SolderedElectronics/USB-UART-CH340C-converter-board-hardware-design/OUTPUTS/V1.2.0/USB-UART CH340C converter board Pinout.png

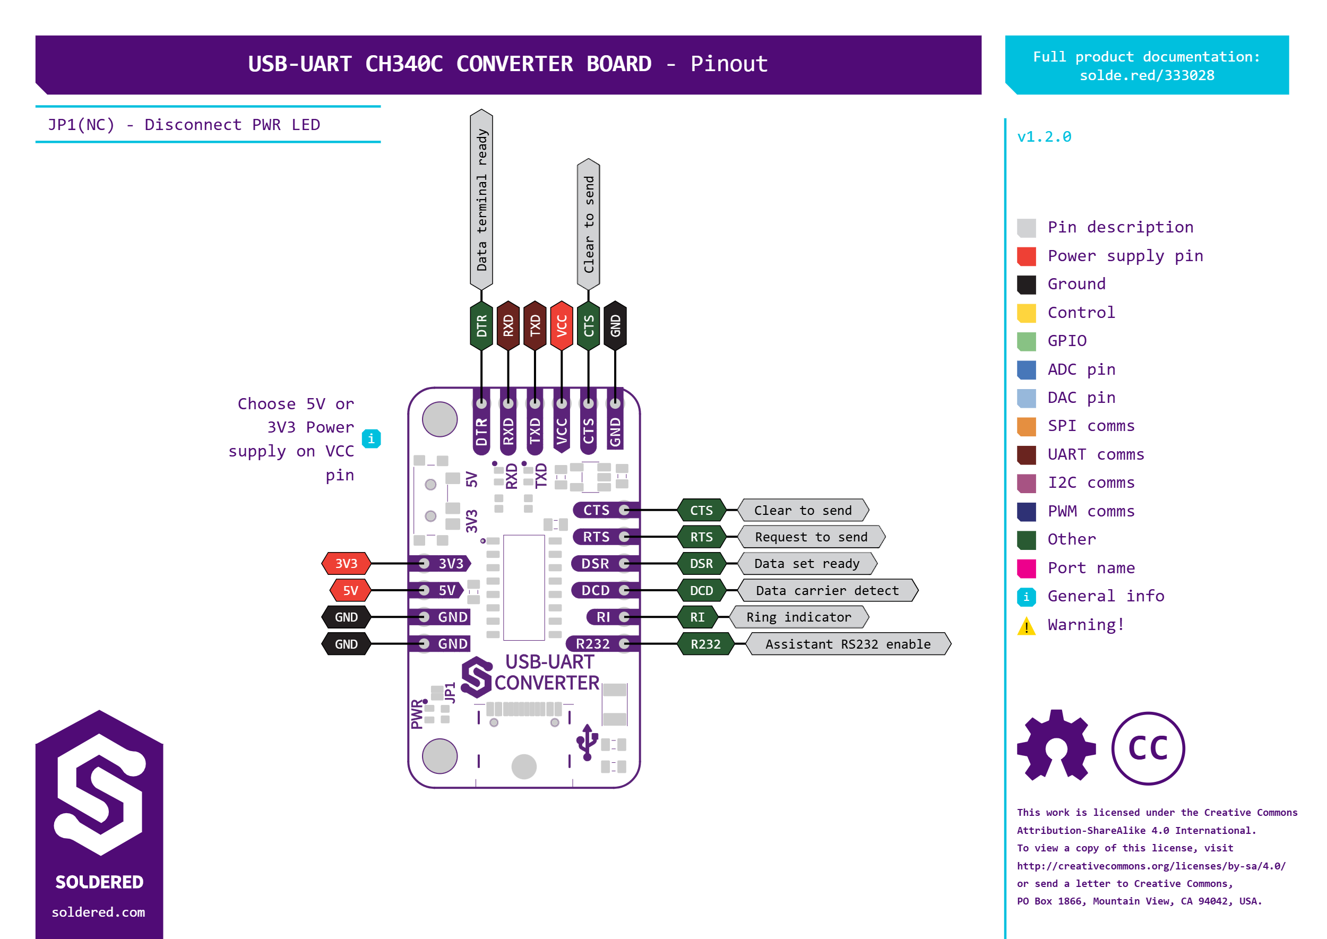
OUTPUTS/V1.2.0/USB-UART CH340C converter board Pinout.png
